SWiT/RobotFightClub/datamatrices/00-01.png

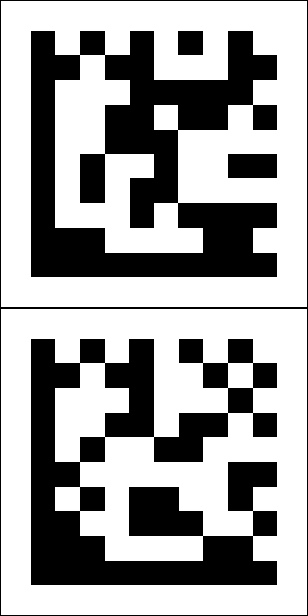
datamatrices/00-01.png
