SWiT/RobotFightClub/datamatrices/00.png

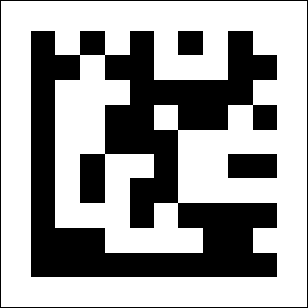
datamatrices/00.png
