SWiT/RobotFightClub/datamatrices/01.png

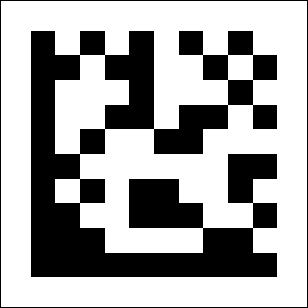
datamatrices/01.png
