SWiT/RobotFightClub/datamatrices/02-03.png

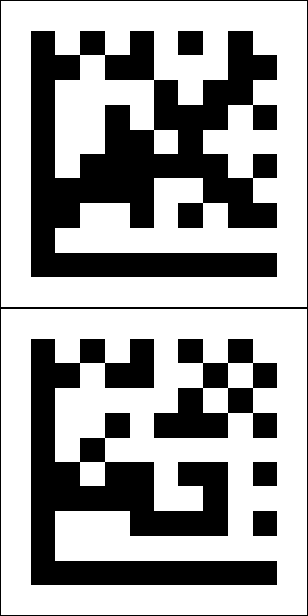
datamatrices/02-03.png
