SWiT/RobotFightClub/datamatrices/02.png

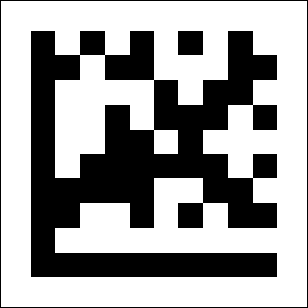
datamatrices/02.png
