SWiT/RobotFightClub/datamatrices/03.png

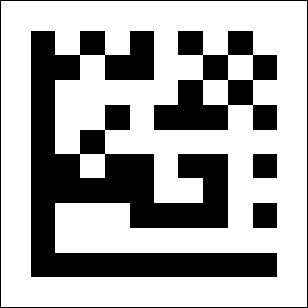
datamatrices/03.png
