SWiT/RobotFightClub/datamatrices/C0.png

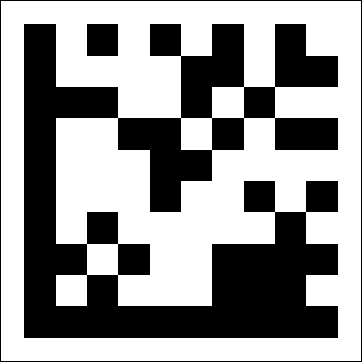
datamatrices/C0.png
