SWiT/RobotFightClub/datamatrices/C1.png

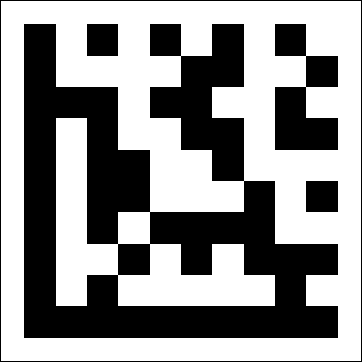
datamatrices/C1.png
