SWiT/RobotFightClub/datamatrices/C2.png

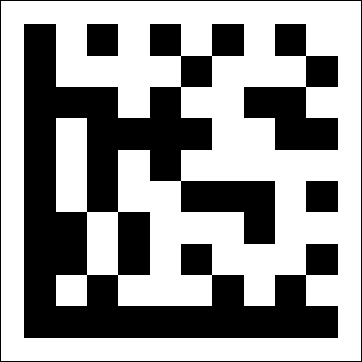
datamatrices/C2.png
