SWiT/RobotFightClub/datamatrices/C4.png

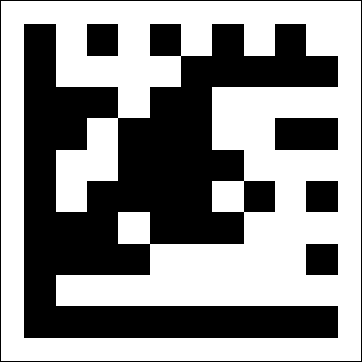
datamatrices/C4.png
