SWiT/RobotFightClub/datamatrices/C5.png

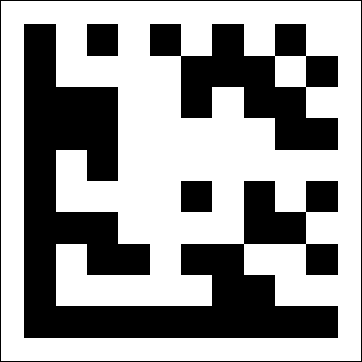
datamatrices/C5.png
