SWiT/RobotFightClub/datamatrices/C6.png

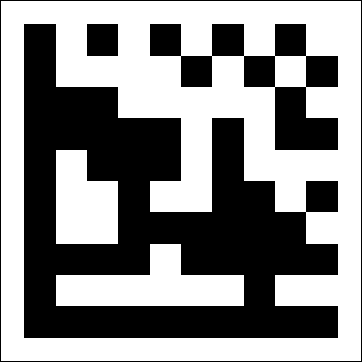
datamatrices/C6.png
