SWiT/RobotFightClub/datamatrices/C7.png

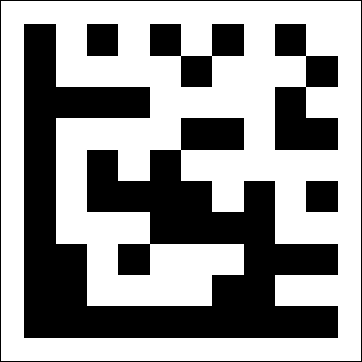
datamatrices/C7.png
