SWiT/RobotFightClub/example_bot_patrol/output_functions.ino

/*
  outputStatus
output important variables to the Serial port
------------------------------------------------------------------------------*/
void outputStatus(){
  //return;
  Serial.println();
  unsigned long now = millis();
  Serial.print("now:");
  Serial.print(now);
  Serial.print("\ttimeToStop:");
  if (timeToStop > now)
  {
    Serial.print(timeToStop-now);
  }else{
    Serial.print(0);
  }
  
  Serial.print("\ttimeLastMessage:");
  Serial.print(now-timeLastMessage);
  Serial.println();
  
  Serial.print("Me: ");
  Serial.print(MY_BOT_ID);
  Serial.print(" (");
  Serial.print(Me[0]);
  Serial.print(", ");
  Serial.print(Me[1]);
  Serial.print(") H");
  Serial.print(Me[2]);
  Serial.print("\tL:");
  Serial.print(speed_L);
  Serial.print("\tR:");
  Serial.print(speed_R);
  Serial.println();
  
  Serial.print("Target: (");
  Serial.print(Target[0]);
  Serial.print(", ");
  Serial.print(Target[1]);
  Serial.print(") H");
  Serial.print(Target[2]);
  Serial.println();
  
  Serial.print("\tdistanceTo:");
  Serial.print(distanceTo);
  Serial.print("\theadingTo:");
  Serial.print(headingTo);
  Serial.print("\trotAmountTo:");
  Serial.print(rotAmountTo);
  Serial.print("\tactionCount:");
  Serial.print(actionCount);
  Serial.println();
  
  for (byte i=0; i<4; i++){
    outputBotStatus(i);
    Serial.println();
  } 
  Serial.println();
        
}

/*
  outputBotStatus
*/
void outputBotStatus(byte i){
  Serial.print(i);
  Serial.print(":(");
  for (byte v=0; v<5; v++) {
    if (v!=0) {Serial.print(",");}
    Serial.print(Bot[i][v]);
    
  }
  Serial.print(")");
}
